Kraken-Jokes/pteron-pcb/images/cookiejar Pteron56.jpg

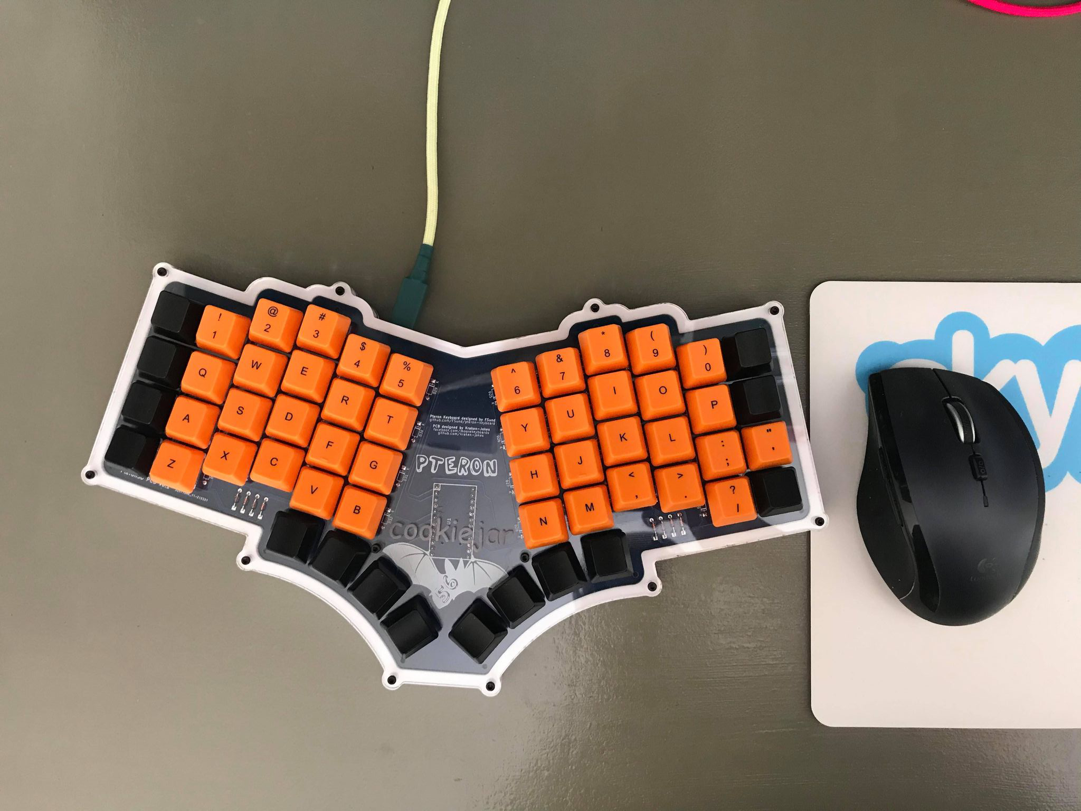
images/cookiejar Pteron56.jpg
