Kraken-Jokes/pteron-pcb/images/Pteron56 Ponder.jpg

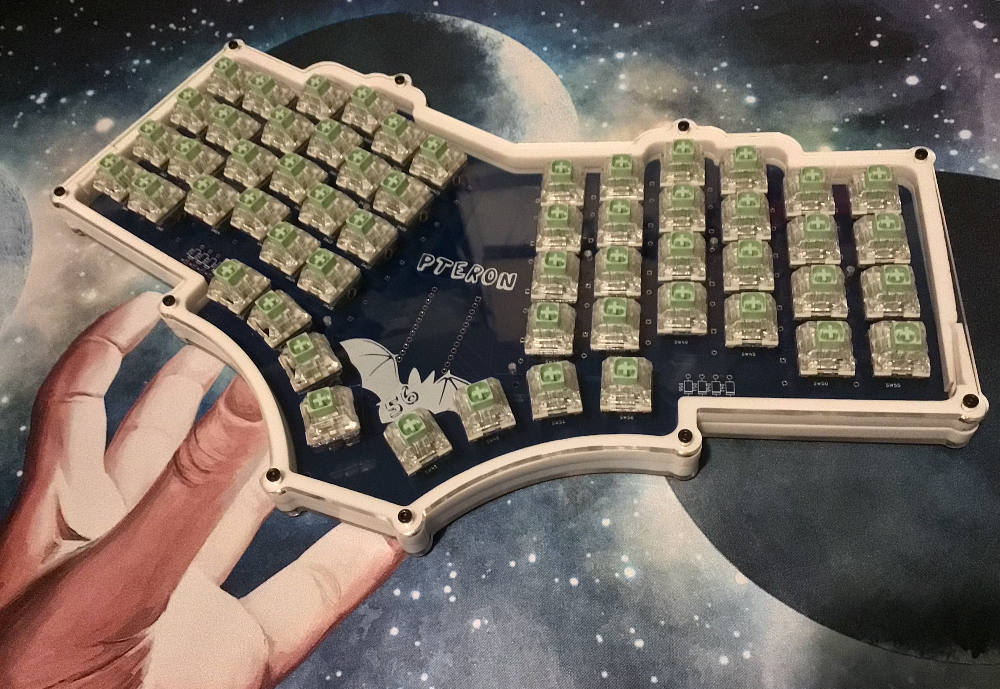
images/Pteron56 Ponder.jpg
