Kraken-Jokes/pteron-pcb/images/Pteron56_HM.jpg

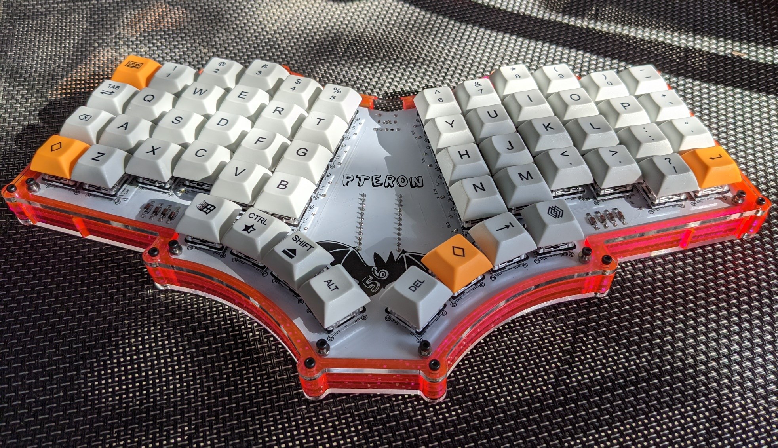
images/Pteron56_HM.jpg
