Kraken-Jokes/pteron-pcb/images/PXL_20210626_202536774_2.jpg

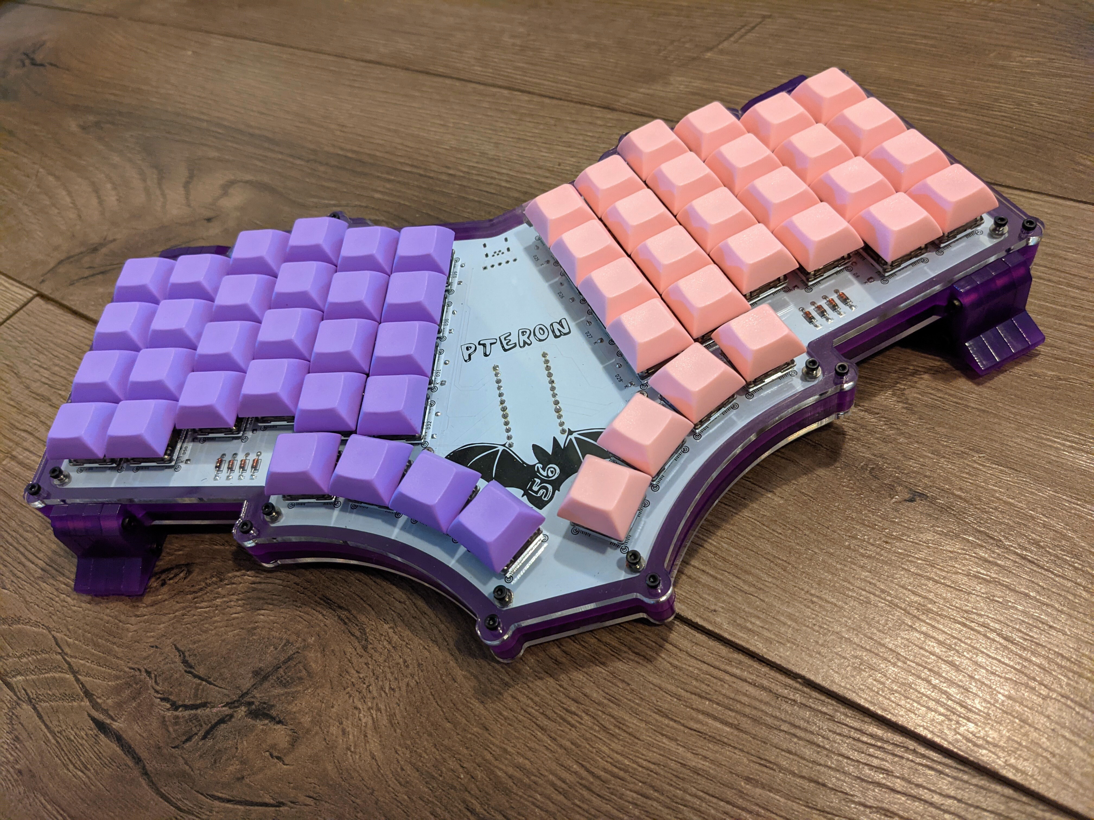
images/PXL_20210626_202536774_2.jpg
