Kraken-Jokes/pteron-pcb/KiCAD and GERBER/Pteron56 w bat.jpg

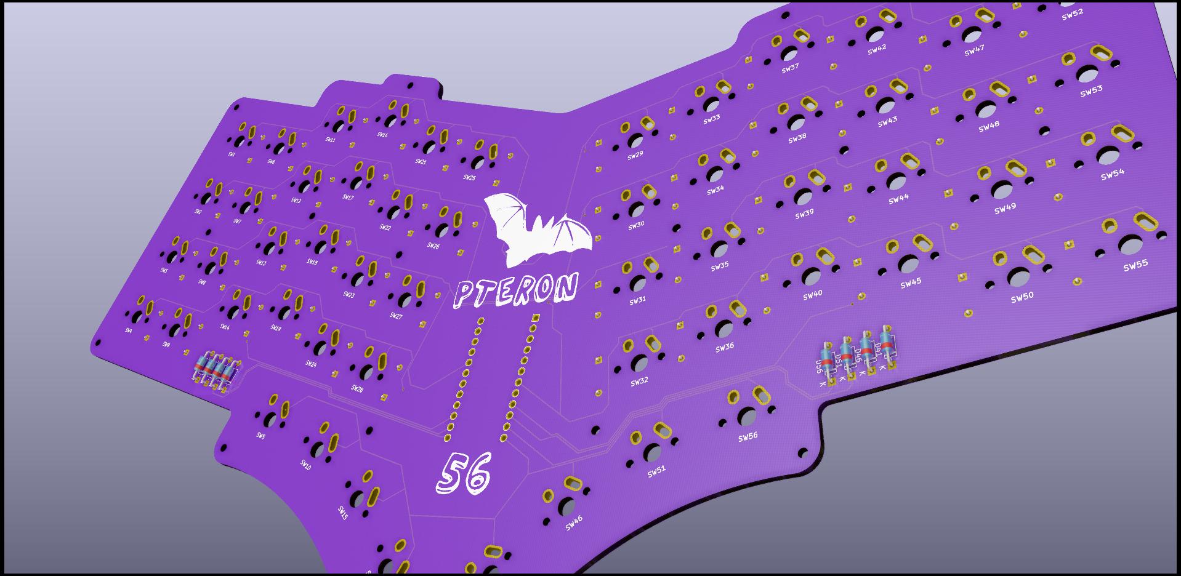
KiCAD and GERBER/Pteron56 w bat.jpg
