Kraken-Jokes/pteron-pcb/KiCAD and GERBER/EXPERIMENTAL/Pteron56v04-NN-palm-E.jpg

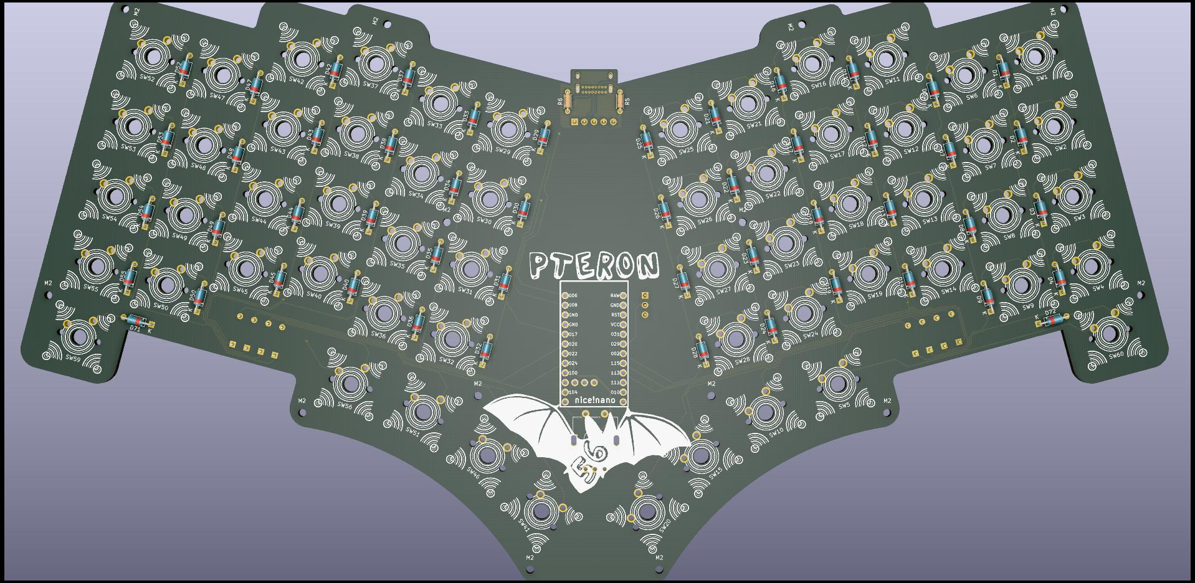
KiCAD and GERBER/EXPERIMENTAL/Pteron56v04-NN-palm-E.jpg
